Blackwolf4183/TFG-SmartPlanter/WebApp/Backend/plant_images/asiento_suegra.jpg

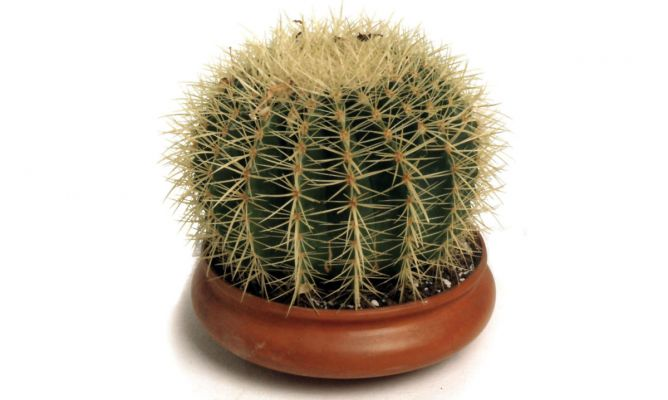
WebApp/Backend/plant_images/asiento_suegra.jpg
