Blackwolf4183/TFG-SmartPlanter/WebApp/Backend/plant_images/cherry.jpg

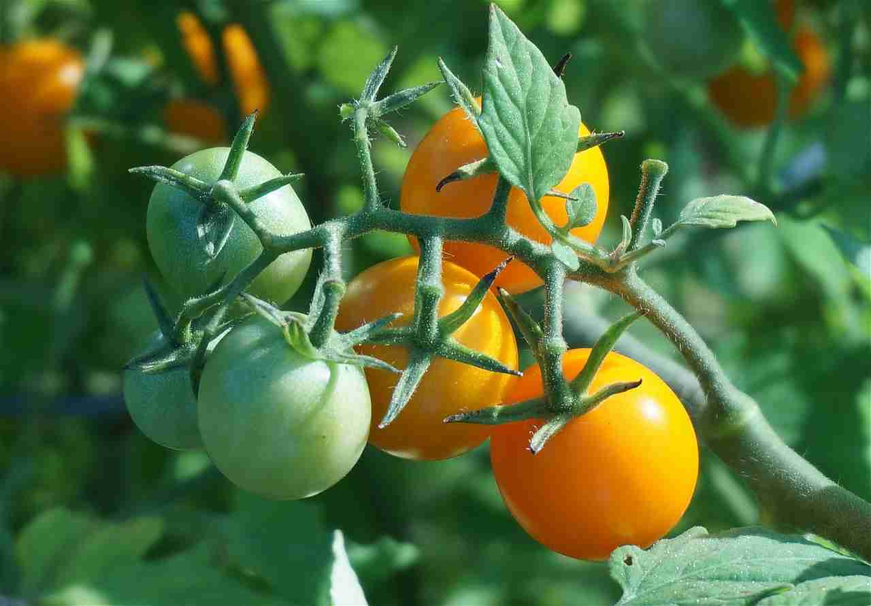
WebApp/Backend/plant_images/cherry.jpg
