Blackwolf4183/TFG-SmartPlanter/WebApp/Backend/plant_images/helechoespada.jpg

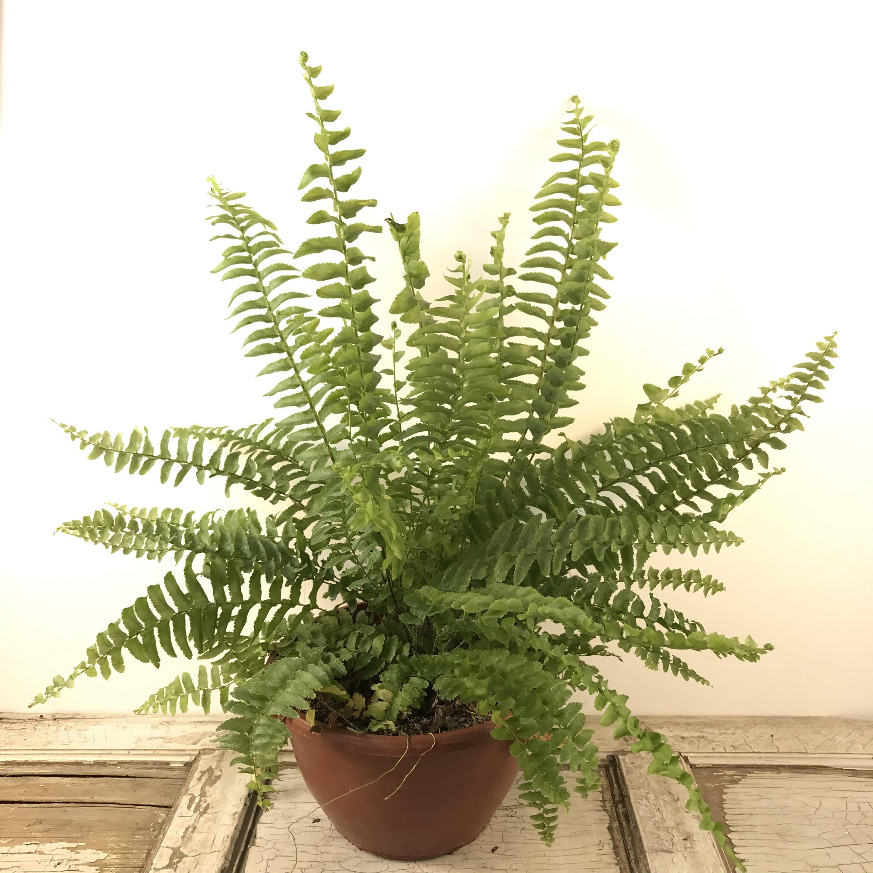
WebApp/Backend/plant_images/helechoespada.jpg
