Blackwolf4183/TFG-SmartPlanter/WebApp/Backend/plant_images/jazmin.jpg

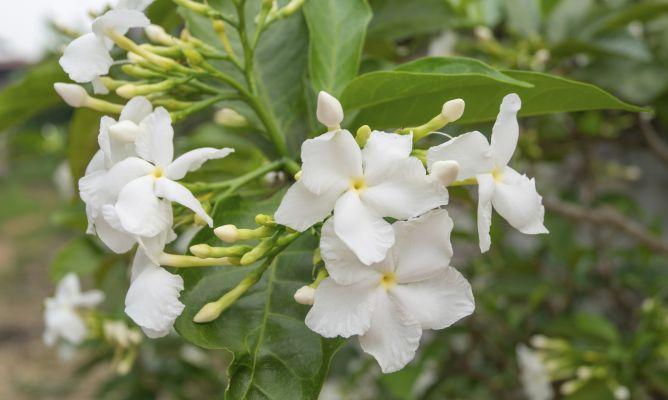
WebApp/Backend/plant_images/jazmin.jpg
