Blackwolf4183/TFG-SmartPlanter/WebApp/Backend/plant_images/reo.jpg

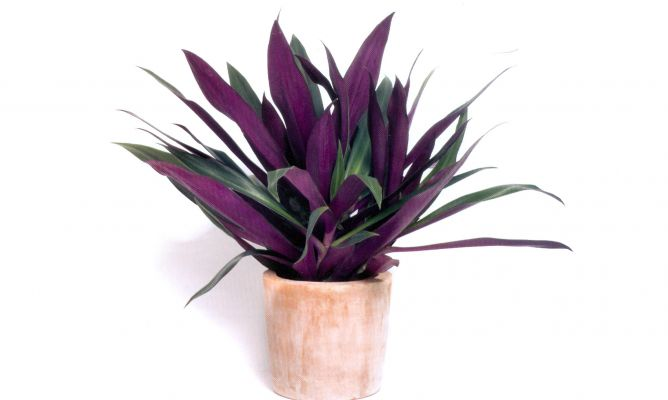
WebApp/Backend/plant_images/reo.jpg
