Blackwolf4183/TFG-SmartPlanter/WebApp/Backend/plant_images/romero.jpg

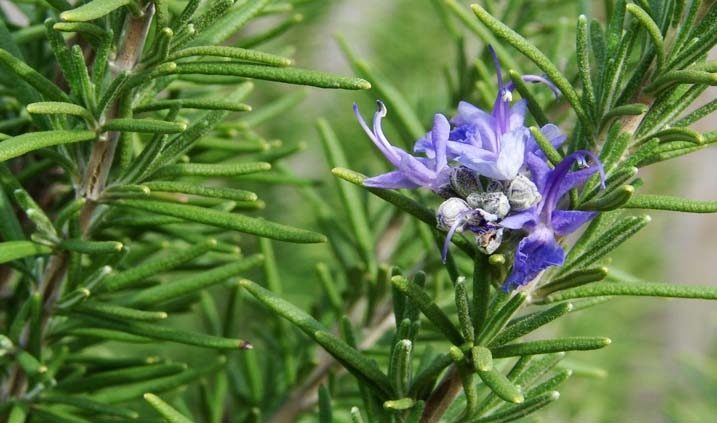
WebApp/Backend/plant_images/romero.jpg
