Blackwolf4183/TFG-SmartPlanter/WebApp/Backend/plant_images/rosario.jpg

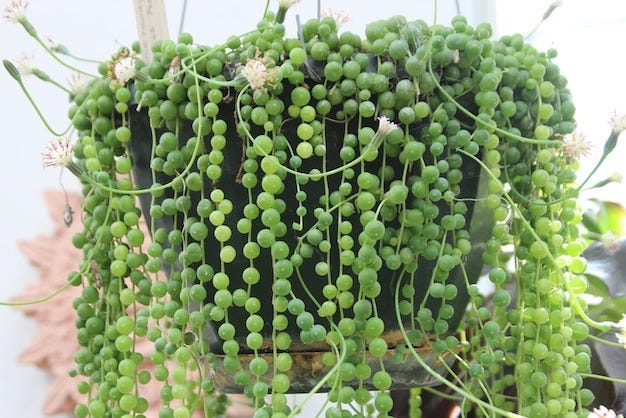
WebApp/Backend/plant_images/rosario.jpg
